acemielektron/abiino/photo1.jpg

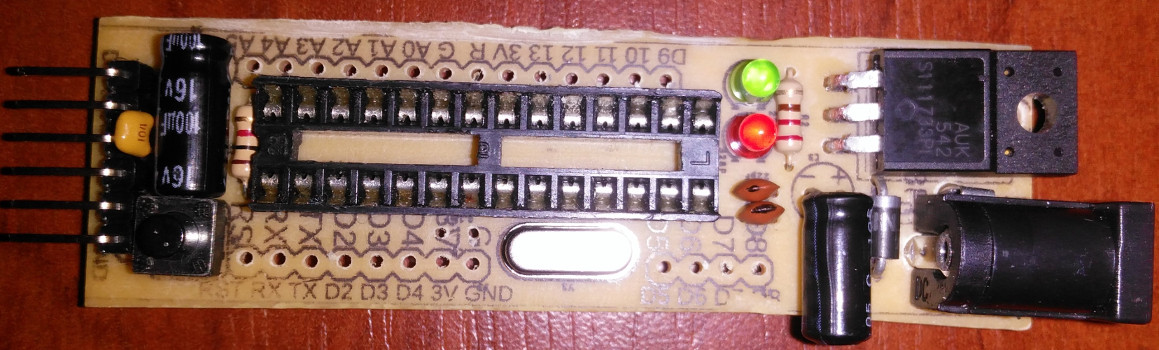
photo1.jpg
