acemielektron/abiino/photo2.jpg

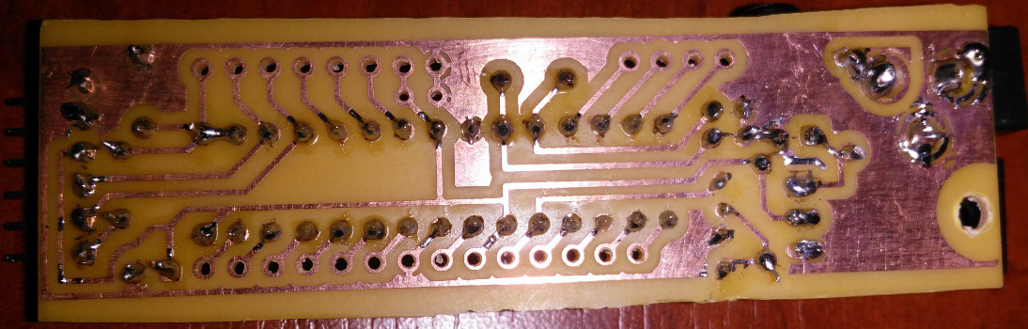
photo2.jpg
