acemielektron/abiino/photo3.jpg

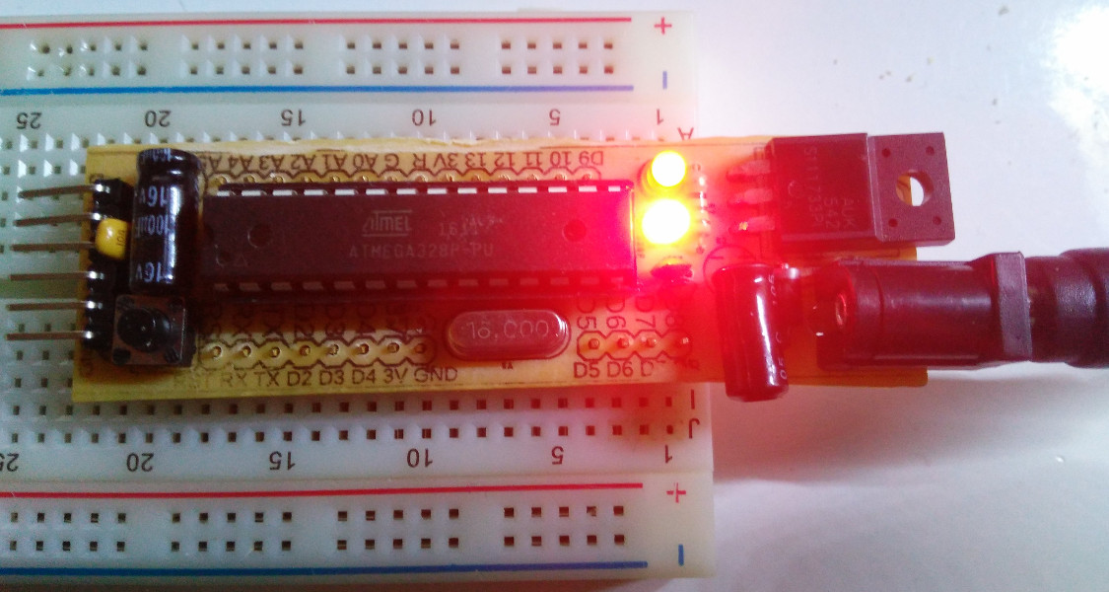
photo3.jpg
